tfeldmann/QlockToo/Documentation/Abbildungen/Elektronik/Taster02.PNG

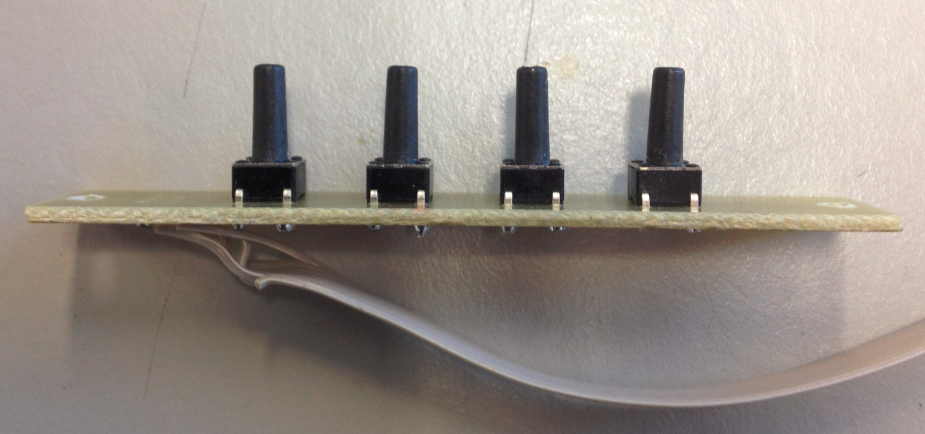
Documentation/Abbildungen/Elektronik/Taster02.PNG
