tfeldmann/QlockToo/Documentation/Abbildungen/Funktionen/Uhrzeit_01.PNG

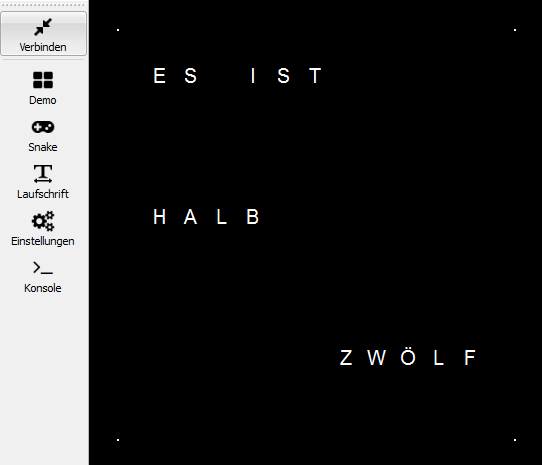
Documentation/Abbildungen/Funktionen/Uhrzeit_01.PNG
