tfeldmann/QlockToo/Documentation/Abbildungen/Konstruktion/Platte01.PNG

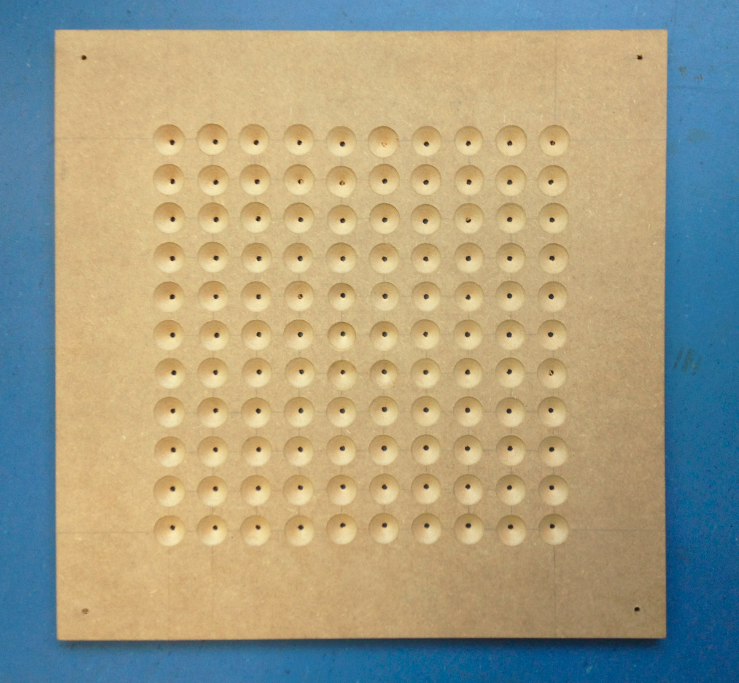
Documentation/Abbildungen/Konstruktion/Platte01.PNG
