tfeldmann/QlockToo/Documentation/Abbildungen/Konstruktion/Ribba.png

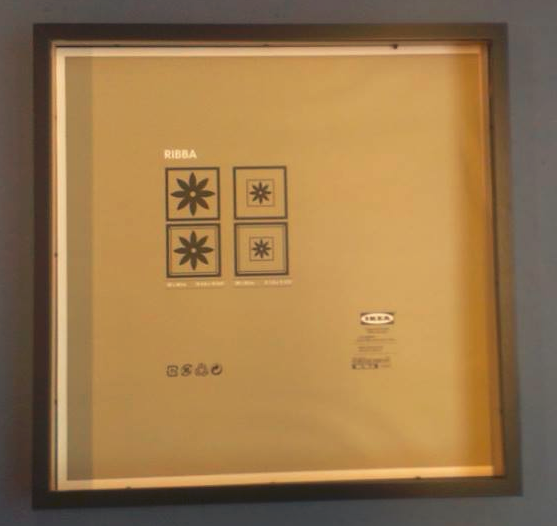
Documentation/Abbildungen/Konstruktion/Ribba.png
