tfeldmann/QlockToo/Documentation/Abbildungen/Software/Bildschirmfoto 2013-12-04 um 14.12.25.png

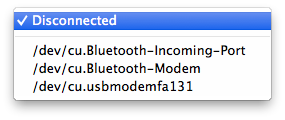
Documentation/Abbildungen/Software/Bildschirmfoto 2013-12-04 um 14.12.25.png
