tfeldmann/QlockToo/Documentation/Abbildungen/Software/Demo/Helix.png

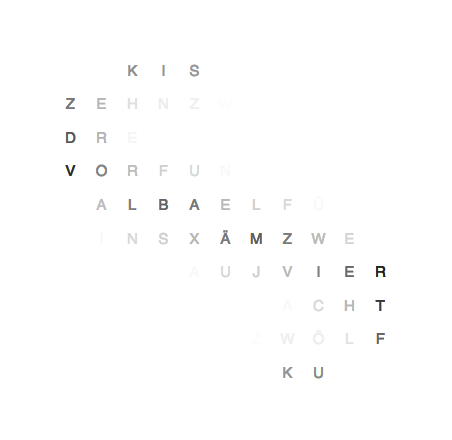
Documentation/Abbildungen/Software/Demo/Helix.png
