tfeldmann/QlockToo/Documentation/Abbildungen/Software/Demo/Laufschrift.png

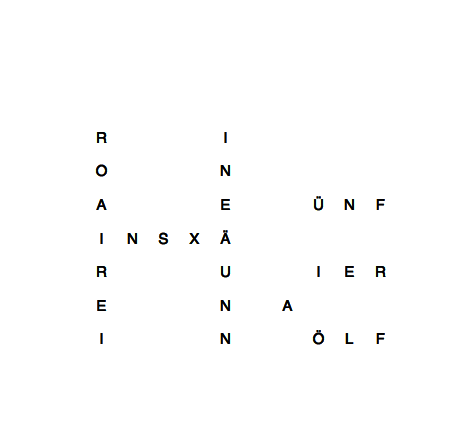
Documentation/Abbildungen/Software/Demo/Laufschrift.png
