tfeldmann/QlockToo/Documentation/Abbildungen/Software/linux.png

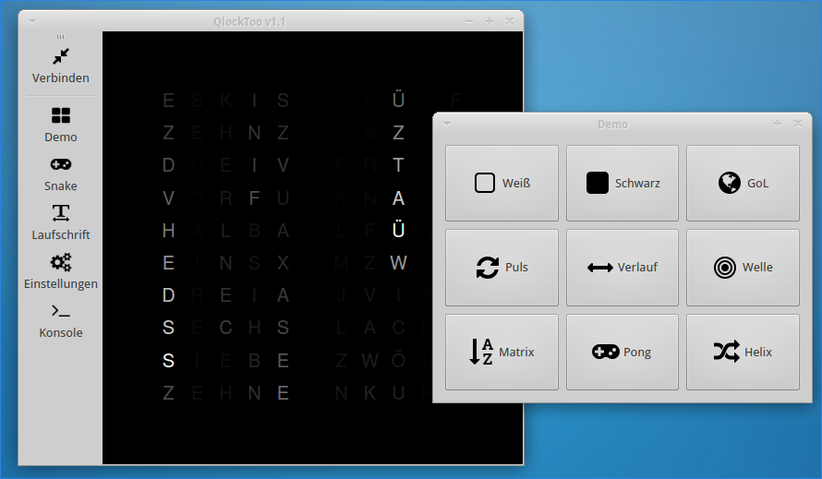
Documentation/Abbildungen/Software/linux.png
