tfeldmann/QlockToo/Documentation/Abbildungen/Software/snake.png

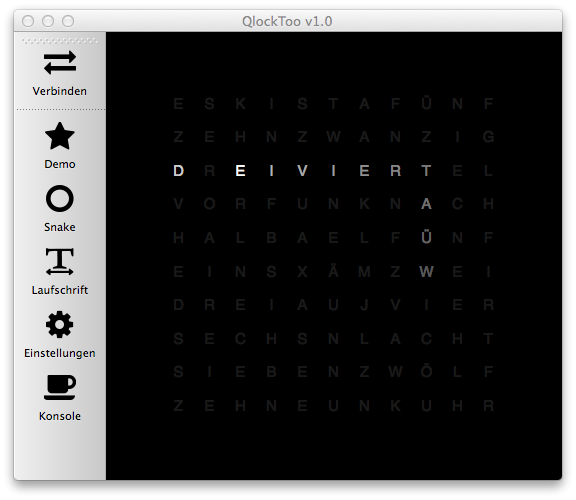
Documentation/Abbildungen/Software/snake.png
