tfeldmann/QlockToo/Documentation/Abbildungen/Software/snake_menu.png

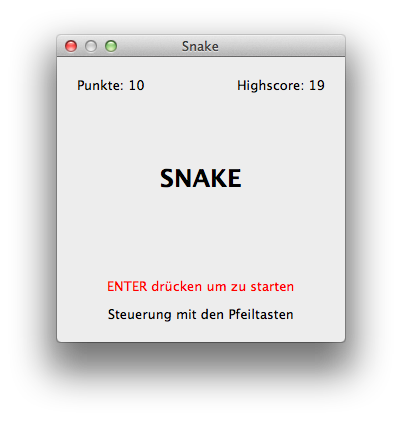
Documentation/Abbildungen/Software/snake_menu.png
